jcassel/Octo-Pendant/Data/Control1.bmp

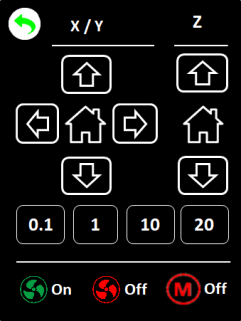
Data/Control1.bmp
