jcassel/Octo-Pendant/Data/ControlMenu.bmp

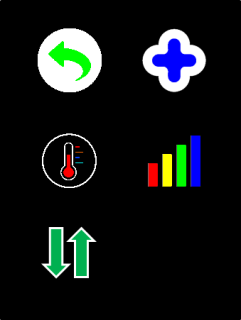
Data/ControlMenu.bmp
