jcassel/Octo-Pendant/Data/FilamentControl.bmp

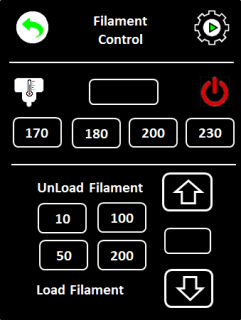
Data/FilamentControl.bmp
