jcassel/Octo-Pendant/Data/Home.bmp

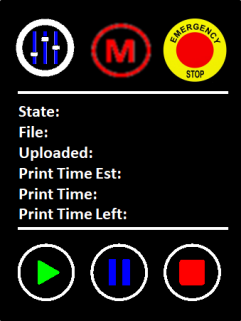
Data/Home.bmp
