jcassel/Octo-Pendant/Data/Level.bmp

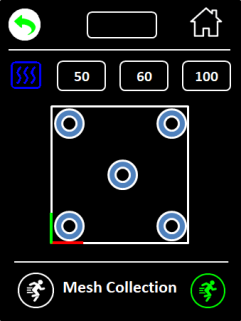
Data/Level.bmp
