jcassel/Octo-Pendant/Data/Temps.bmp

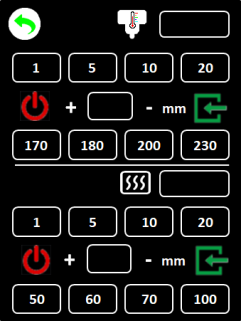
Data/Temps.bmp
